Rattus-ukrizovany/RattusBoard/keyboards/rattusboard/keymaps/vial/config.h

// Copyright 2024 RattusBoard Project
// SPDX-License-Identifier: GPL-3.0-or-later

#pragma once

// VIAL Configuration
#define VIAL_KEYBOARD_UID {0x12, 0x34, 0x56, 0x78, 0x90, 0x12, 0x34, 0xEF}

// Unlock method - use any key combination
#define VIAL_UNLOCK_COMBO_ROWS { 0, 2 }
#define VIAL_UNLOCK_COMBO_COLS { 0, 5 }
